dkgrizzly/GreenSCSI/src/partitions.ino

#if 0
#include "config.h"
#include "cmd.h"

typedef struct PartType_s {
  unsigned char Type;
  const char *Name;
} PartType_t;
PartType_t PartType[] = {
  { 0x00, "Empty" },
  { 0x01, "FAT12" },
  { 0x04, "FAT16 <32MB" },
  { 0x05, "Extended" },
  { 0x06, "FAT16 >32MB" },
  { 0x07, "NTFS" },
  { 0x0b, "FAT32" },
  { 0x0c, "FAT32 LBA" },
  { 0x0e, "FAT16 LBA" },
  { 0x0f, "Extended LBA" },
  { 0xf8, "TinySCSI Disk LUN" },
  { 0xf9, "TinySCSI Optical LUN" },
  { 0xff, NULL }
};
#endif

/* 
 *  Public domain MBR boot manager from https://github.com/egormkn/mbr-boot-manager
 */
uint8_t mbr_bin[512] = {
  0xFA, 0xBC, 0x00, 0x7C, 0x31, 0xC0, 0x8E, 0xD0, 0x8E, 0xC0, 0x8E, 0xD8, 0x52, 0xBE, 0x00, 0x7C,
  0xBF, 0x00, 0x06, 0xB9, 0x00, 0x02, 0xFC, 0xF3, 0xA4, 0xE9, 0x00, 0x8A, 0xFB, 0xB8, 0x03, 0x00,
  0xCD, 0x10, 0xB8, 0x00, 0x06, 0xB7, 0x02, 0x31, 0xC9, 0xBA, 0x4F, 0x18, 0xCD, 0x10, 0xB8, 0x03,
  0x01, 0xB9, 0x05, 0x01, 0xCD, 0x10, 0xB9, 0x04, 0x00, 0xBD, 0xEE, 0x07, 0x31, 0xDB, 0x55, 0x80,
  0x7E, 0x00, 0x80, 0x75, 0x02, 0x88, 0xCB, 0xB4, 0x02, 0xBA, 0x22, 0x08, 0x00, 0xCE, 0xCD, 0x10,
  0xBE, 0x8D, 0x07, 0xE8, 0x2B, 0x01, 0xB0, 0x30, 0x00, 0xC8, 0xB4, 0x0E, 0xCD, 0x10, 0x38, 0xCB,
  0x75, 0x06, 0xBE, 0x98, 0x07, 0xE8, 0x19, 0x01, 0x5D, 0x83, 0xED, 0x10, 0xE2, 0xD0, 0x38, 0xFB,
  0x75, 0x03, 0x43, 0xEB, 0x0A, 0xB4, 0x02, 0xCD, 0x16, 0x24, 0x03, 0x38, 0xF8, 0x74, 0x51, 0xB4,
  0x02, 0xBA, 0x20, 0x08, 0x00, 0xDE, 0xCD, 0x10, 0x88, 0xFC, 0xCD, 0x16, 0x3D, 0x00, 0x48, 0x74,
  0x11, 0x3D, 0x00, 0x50, 0x74, 0x14, 0x3D, 0x1B, 0x01, 0x74, 0x2D, 0x3D, 0x0D, 0x1C, 0x74, 0x30,
  0xEB, 0xDD, 0x80, 0xFB, 0x01, 0x7E, 0x01, 0x4B, 0xEB, 0xD5, 0x80, 0xFB, 0x04, 0x73, 0x01, 0x43,
  0xEB, 0xCD, 0xBE, 0x9D, 0x07, 0xE8, 0xC9, 0x00, 0xB8, 0x00, 0x86, 0xB9, 0x2D, 0x00, 0x31, 0xD2,
  0xCD, 0x15, 0xEB, 0x04, 0xCD, 0x18, 0xCD, 0x19, 0xEA, 0x00, 0x00, 0xFF, 0xFF, 0xF4, 0xEB, 0xFD,
  0x53, 0xB4, 0x02, 0xBA, 0x01, 0x01, 0xCD, 0x10, 0xB8, 0x00, 0x06, 0xB7, 0x02, 0x31, 0xC9, 0xBA,
  0x4F, 0x18, 0xCD, 0x10, 0xBD, 0xAE, 0x07, 0x5B, 0xC1, 0xE3, 0x04, 0x01, 0xDD, 0x5A, 0x88, 0x56,
  0x00, 0x55, 0xC6, 0x46, 0x11, 0x05, 0x88, 0x7E, 0x10, 0xB4, 0x41, 0xBB, 0xAA, 0x55, 0xCD, 0x13,
  0x5D, 0x72, 0x0F, 0x81, 0xFB, 0x55, 0xAA, 0x75, 0x09, 0xF7, 0xC1, 0x01, 0x00, 0x74, 0x03, 0xFE,
  0x46, 0x10, 0x66, 0x60, 0x80, 0x7E, 0x0A, 0x00, 0x74, 0x20, 0x66, 0x6A, 0x00, 0x66, 0xFF, 0x76,
  0x08, 0x6A, 0x00, 0x68, 0x00, 0x7C, 0x6A, 0x01, 0x6A, 0x10, 0xB4, 0x42, 0x8A, 0x56, 0x00, 0x89,
  0xE6, 0xCD, 0x13, 0x9F, 0x83, 0xC4, 0x10, 0x9E, 0xEB, 0x14, 0xB8, 0x01, 0x02, 0xBB, 0x00, 0x7C,
  0x8A, 0x56, 0x00, 0x8A, 0x76, 0x01, 0x8A, 0x4E, 0x02, 0x8A, 0x6E, 0x03, 0xCD, 0x13, 0x66, 0x61,
  0x73, 0x12, 0xFE, 0x4E, 0x11, 0x0F, 0x84, 0x59, 0xFF, 0x55, 0x30, 0xE4, 0x8A, 0x56, 0x00, 0xCD,
  0x13, 0x5D, 0xEB, 0xAE, 0x81, 0x3E, 0xFE, 0x7D, 0x55, 0xAA, 0x0F, 0x85, 0x44, 0xFF, 0x83, 0x3E,
  0x00, 0x7C, 0x00, 0x0F, 0x84, 0x3B, 0xFF, 0x8B, 0x56, 0x00, 0x30, 0xF6, 0xEA, 0x00, 0x7C, 0x00,
  0x00, 0xB4, 0x0E, 0xAC, 0x3C, 0x00, 0x74, 0x04, 0xCD, 0x10, 0xEB, 0xF7, 0xC3, 0x50, 0x61, 0x72,
  0x74, 0x69, 0x74, 0x69, 0x6F, 0x6E, 0x20, 0x00, 0x20, 0x28, 0x41, 0x29, 0x00, 0x42, 0x6F, 0x6F,
  0x74, 0x20, 0x73, 0x65, 0x63, 0x74, 0x6F, 0x72, 0x20, 0x65, 0x72, 0x72, 0x6F, 0x72, 0x0D, 0x0A,
  0x00, 0x00, 0x00, 0x00, 0x00, 0x00, 0x00, 0x00, 0x78, 0x56, 0x34, 0x12, 0x00, 0x00, 0x00, 0x00,
  0x00, 0x00, 0x00, 0x00, 0x00, 0x00, 0x00, 0x00, 0x00, 0x00, 0x00, 0x00, 0x00, 0x00, 0x00, 0x00,
  0x00, 0x00, 0x00, 0x00, 0x00, 0x00, 0x00, 0x00, 0x00, 0x00, 0x00, 0x00, 0x00, 0x00, 0x00, 0x00,
  0x00, 0x00, 0x00, 0x00, 0x00, 0x00, 0x00, 0x00, 0x00, 0x00, 0x00, 0x00, 0x00, 0x00, 0x00, 0x00,
  0x00, 0x00, 0x00, 0x00, 0x00, 0x00, 0x00, 0x00, 0x00, 0x00, 0x00, 0x00, 0x00, 0x00, 0x55, 0xAA
};
